arduino12/uv_bicycle/src/arduino_to_uv/heb_ger_11x13.h

/*
	* heb_ger_11x13.h
	* Created with GlcdToMatrixFontConverter
	* written by Arad Eizen 2014
	*  
	* https://www.youtube.com/channel/UC5gCXtbBpkhmnDZb2CdSwrQ
	* a.e.tec.inc@gmail.com
	*  
	* Font Name           : heb_ger_11x13
	* Date                : 09/11/2017
	* Font size in bytes  : 1985
	* Font width          : 11
	* Font height         : 13
	* Font first char     : 32
	* Font char count     : 130
*/

static const uint8_t heb_ger_11x13[] PROGMEM = {
	0x0D, // Height
	0x20, // First Char
	0x82, // Char Count

	 // Characters Table: [Char Width, MSB Position, LSB Position] * Char Count
	0x07,0x01,0x89,
	0x02,0x01,0x97,
	0x04,0x01,0x9B,
	0x08,0x01,0xA3,
	0x06,0x01,0xB3,
	0x0B,0x01,0xBF,
	0x08,0x01,0xD5,
	0x02,0x01,0xE5,
	0x05,0x01,0xE9,
	0x04,0x01,0xF3,
	0x06,0x01,0xFB,
	0x07,0x02,0x07,
	0x02,0x02,0x15,
	0x04,0x02,0x19,
	0x02,0x02,0x21,
	0x05,0x02,0x25,
	0x06,0x02,0x2F,
	0x06,0x02,0x3B,
	0x06,0x02,0x47,
	0x06,0x02,0x53,
	0x06,0x02,0x5F,
	0x06,0x02,0x6B,
	0x06,0x02,0x77,
	0x06,0x02,0x83,
	0x06,0x02,0x8F,
	0x06,0x02,0x9B,
	0x03,0x02,0xA7,
	0x03,0x02,0xAD,
	0x08,0x02,0xB3,
	0x08,0x02,0xC3,
	0x08,0x02,0xD3,
	0x05,0x02,0xE3,
	0x0B,0x02,0xED,
	0x07,0x03,0x03,
	0x06,0x03,0x11,
	0x07,0x03,0x1D,
	0x07,0x03,0x2B,
	0x06,0x03,0x39,
	0x06,0x03,0x45,
	0x07,0x03,0x51,
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

	 // Characters Data: [Data...] * Char Count
	0x00,0x00,0x00,0x00,0x00,0x00,0x00,0x00,0x00,0x00,0x00,0x00,0x00,0x00,
	0x00,0x00,0x7E,0x03,
	0x00,0x00,0x0F,0x00,0x00,0x00,0x0F,0x00,
	0x00,0x00,0x40,0x00,0x48,0x03,0xF8,0x00,0x4E,0x03,0xF8,0x00,0x4E,0x00,0x08,0x00,
	0x18,0x02,0x24,0x02,0xFF,0x0F,0x44,0x02,0x44,0x02,0x84,0x01,
	0x00,0x00,0x1C,0x00,0x22,0x00,0x22,0x02,0x9C,0x01,0x60,0x00,0x10,0x00,0xCC,0x01,0x22,0x02,0x20,0x02,0xC0,0x01,
	0xCC,0x01,0x32,0x02,0x22,0x02,0x22,0x02,0x52,0x02,0x8C,0x01,0xE0,0x01,0x00,0x02,
	0x00,0x00,0x0F,0x00,
	0x00,0x00,0xF0,0x01,0x0C,0x06,0x02,0x08,0x01,0x10,
	0x01,0x10,0x02,0x08,0x0C,0x06,0xF0,0x01,
	0x00,0x00,0x0A,0x00,0x04,0x00,0x1F,0x00,0x04,0x00,0x0A,0x00,
	0x20,0x00,0x20,0x00,0x20,0x00,0xFC,0x01,0x20,0x00,0x20,0x00,0x20,0x00,
	0x00,0x08,0x00,0x07,
	0x20,0x00,0x20,0x00,0x20,0x00,0x20,0x00,
	0x00,0x00,0x00,0x03,
	0x00,0x0C,0x80,0x03,0x60,0x00,0x1C,0x00,0x03,0x00,
	0xFC,0x01,0x02,0x02,0x02,0x02,0x02,0x02,0x02,0x02,0xFC,0x01,
	0x00,0x00,0x04,0x02,0x04,0x02,0xFE,0x03,0x00,0x02,0x00,0x02,
	0x04,0x03,0x82,0x02,0x42,0x02,0x42,0x02,0x22,0x02,0x1C,0x02,
	0x04,0x01,0x02,0x02,0x22,0x02,0x22,0x02,0x22,0x02,0xDC,0x01,
	0x60,0x00,0x50,0x00,0x48,0x00,0x44,0x00,0xFE,0x03,0x40,0x00,
	0x1E,0x01,0x12,0x02,0x12,0x02,0x12,0x02,0x12,0x02,0xE2,0x01,
	0xF8,0x01,0x14,0x02,0x12,0x02,0x12,0x02,0x12,0x02,0xE0,0x01,
	0x02,0x00,0x02,0x02,0x82,0x01,0x62,0x00,0x1A,0x00,0x06,0x00,
	0xDC,0x01,0x22,0x02,0x22,0x02,0x22,0x02,0x22,0x02,0xDC,0x01,
	0x3C,0x00,0x42,0x02,0x42,0x02,0x42,0x02,0x42,0x01,0xFC,0x00,
	0x00,0x00,0x00,0x00,0x18,0x03,
	0x00,0x00,0x00,0x08,0x18,0x07,
	0x00,0x00,0x20,0x00,0x20,0x00,0x50,0x00,0x50,0x00,0x88,0x00,0x88,0x00,0x04,0x01,
	0x00,0x00,0x90,0x00,0x90,0x00,0x90,0x00,0x90,0x00,0x90,0x00,0x90,0x00,0x90,0x00,
	0x00,0x00,0x04,0x01,0x88,0x00,0x88,0x00,0x50,0x00,0x50,0x00,0x20,0x00,0x20,0x00,
	0x04,0x00,0x42,0x03,0x22,0x00,0x12,0x00,0x0C,0x00,
	0xF0,0x00,0x0C,0x03,0x04,0x02,0xF2,0x04,0x0A,0x05,0x0A,0x05,0x0A,0x05,0xFA,0x05,0x04,0x01,0x0C,0x01,0xF0,0x00,
	0x00,0x03,0xE0,0x00,0x98,0x00,0x86,0x00,0x98,0x00,0xE0,0x00,0x00,0x03,
	0xFE,0x03,0x22,0x02,0x22,0x02,0x22,0x02,0x3C,0x02,0xC0,0x01,
	0xF8,0x00,0x04,0x01,0x02,0x02,0x02,0x02,0x02,0x02,0x02,0x02,0x04,0x01,
	0xFE,0x03,0x02,0x02,0x02,0x02,0x02,0x02,0x02,0x02,0x04,0x01,0xF8,0x00,
	0xFE,0x03,0x22,0x02,0x22,0x02,0x22,0x02,0x22,0x02,0x22,0x02,
	0xFE,0x03,0x22,0x00,0x22,0x00,0x22,0x00,0x22,0x00,0x22,0x00,
	0xF8,0x00,0x04,0x01,0x02,0x02,0x02,0x02,0x42,0x02,0x42,0x02,0xC4,0x03,
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
};
