arduino12/uv_bicycle/src/arduino_to_uv/fix_texts.h

#ifndef FIX_TEXTS_H
#define FIX_TEXTS_H

const char * FIX_TEXTS[] = {
#if LANGUAGE_CODE == 0
	"אופניים פוטוכרומיות",
	"מוזיאון המדע בירושלים..!",
	"o_o  ^.^  O..O",
	"נבנה על ידי אבישי וארד!",
	"מאתיים שנה להמצאת האופניים",
	"לארד ויוסי כל הכבוד",
	"לברוך כל הכבוד",
	"יפה שתיקה לחכמים",
	"אם אין קמח אין לחם",
	"אין הביישן למד",
	"אנשים הם כמו אופניים בסוף הכידון מחליד",
	"אנשים טובים יש בכל פינה אבל העולם הוא עגול",
	"כבד את אביך ואת אמך",
	"אל תאמר לכשאפנה אשנה שמא לא תפנה",
	"ילדים הזהרו מעצי באובב",
	"שלחו מסרון ל 3740112-350",
	"תערוכת אופניים במוזיאון המדע",
#else
	"Universum Bremen",
	"Hergestellt In Israel",
	"Mir Ist Schwindlig",
	"Photochromatische Fahrräder",
	"Sende Mir Eine SMS",
	"Frieden Und Liebe",
	"Wo sind die Bremsen ?!",
	"Wiener Straße 1a",
	"o_o  ^.^  O..O",
	"Photochromatic Bicycles",
	"Peace And Love",
	"Send Me SMS ! ! !",
	"I'm Getting Dizzy",
	"Text Me . . .",
	"Where Are The Brakes ?!",
	"Made In Israel",
#endif
};

#endif /* FIX_TEXTS_H */
